gabrieltoribiopereira/e-ink-display/images/image_2.png

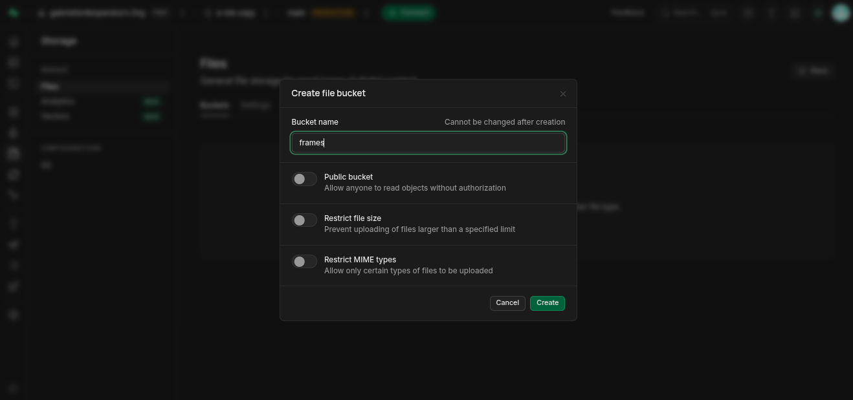
images/image_2.png
