gabrieltoribiopereira/e-ink-display/images/WhatsApp Image 2026-08-20 at 17.56.26.jpeg

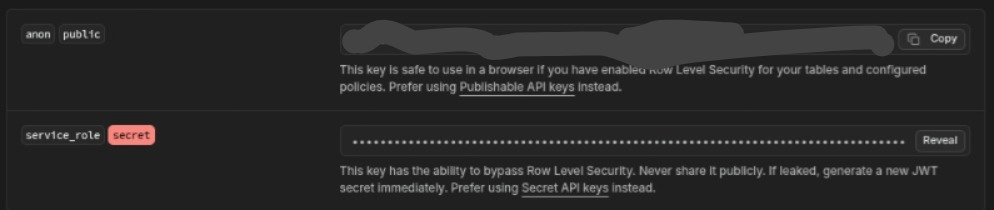
images/WhatsApp Image 2026-08-20 at 17.56.26.jpeg
